RaheelFarouk/ece1895-DesignProject3/Datasheets and Reference Docs/Arduino Ethernet Shield v2.0/Images/Screenshot 2022-10-31 183120.png

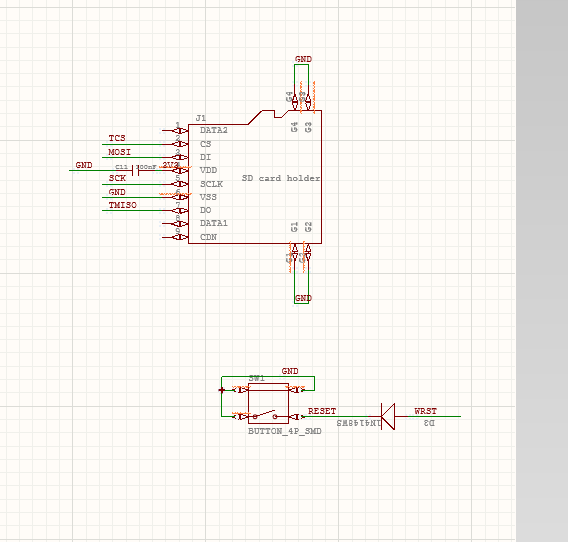
Datasheets and Reference Docs/Arduino Ethernet Shield v2.0/Images/Screenshot 2022-10-31 183120.png
