RaheelFarouk/ece1895-DesignProject3/Media/PXL_20221130_163156786.MP.jpg

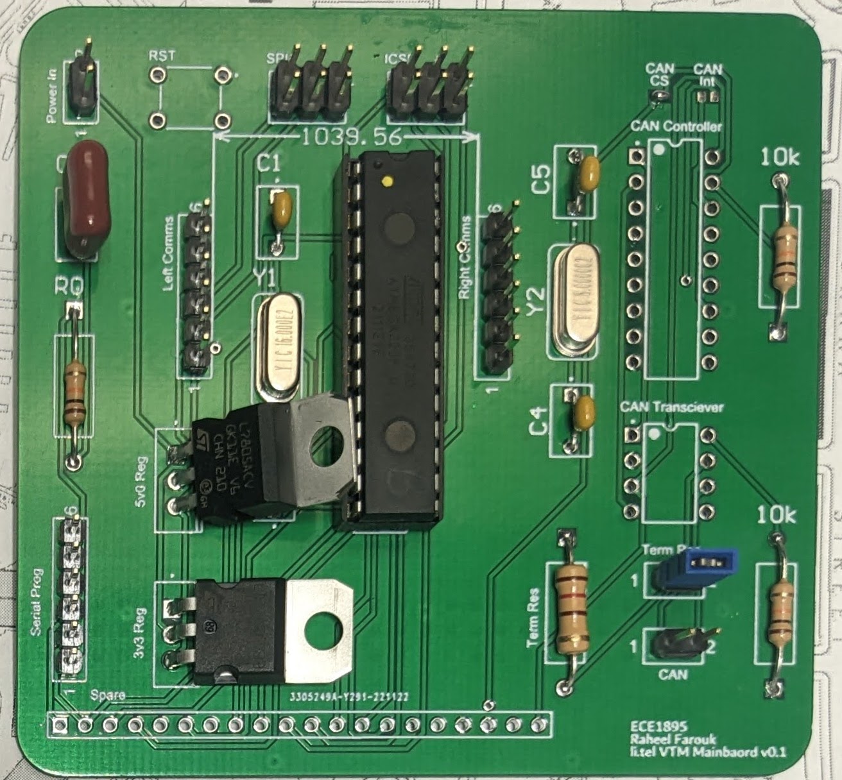
Media/PXL_20221130_163156786.MP.jpg
