RaheelFarouk/ece1895-DesignProject3/Media/PXL_20221209_193834264.jpg

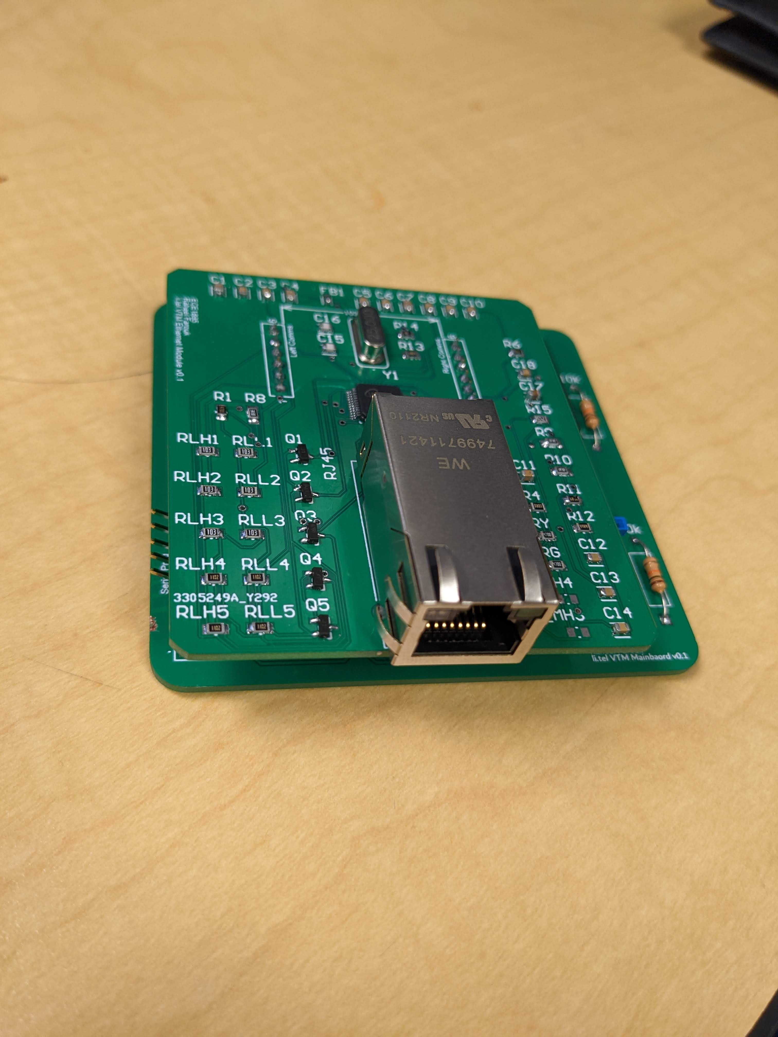
Media/PXL_20221209_193834264.jpg
