RaheelFarouk/ece1895-DesignProject3/Media/PXL_20221214_212605422.jpg

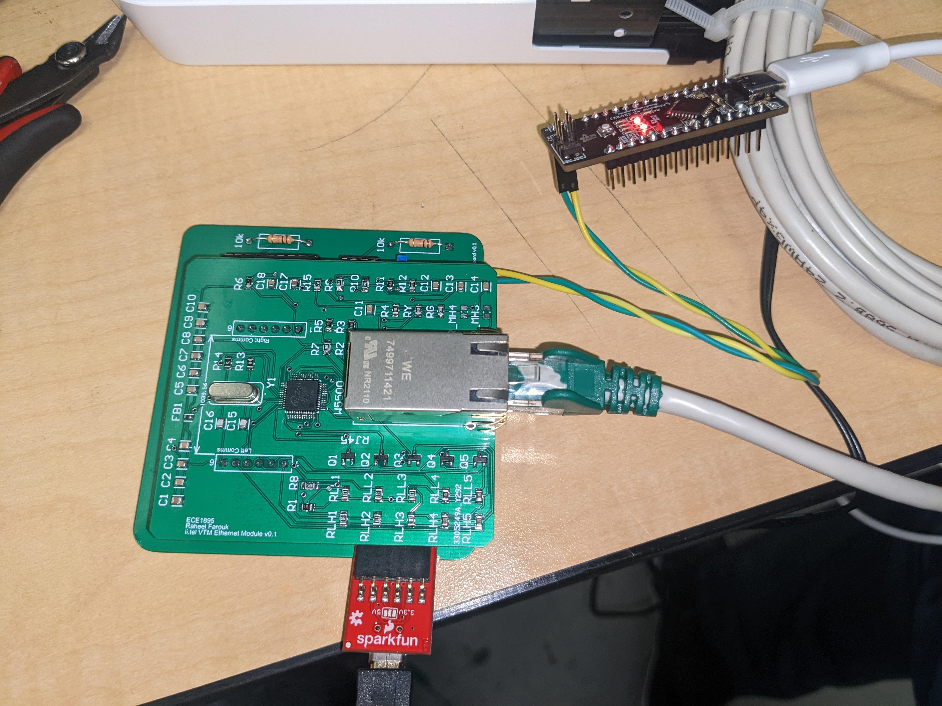
Media/PXL_20221214_212605422.jpg
