RaheelFarouk/ece1895-DesignProject3/Media/PXL_20221214_212624482.jpg

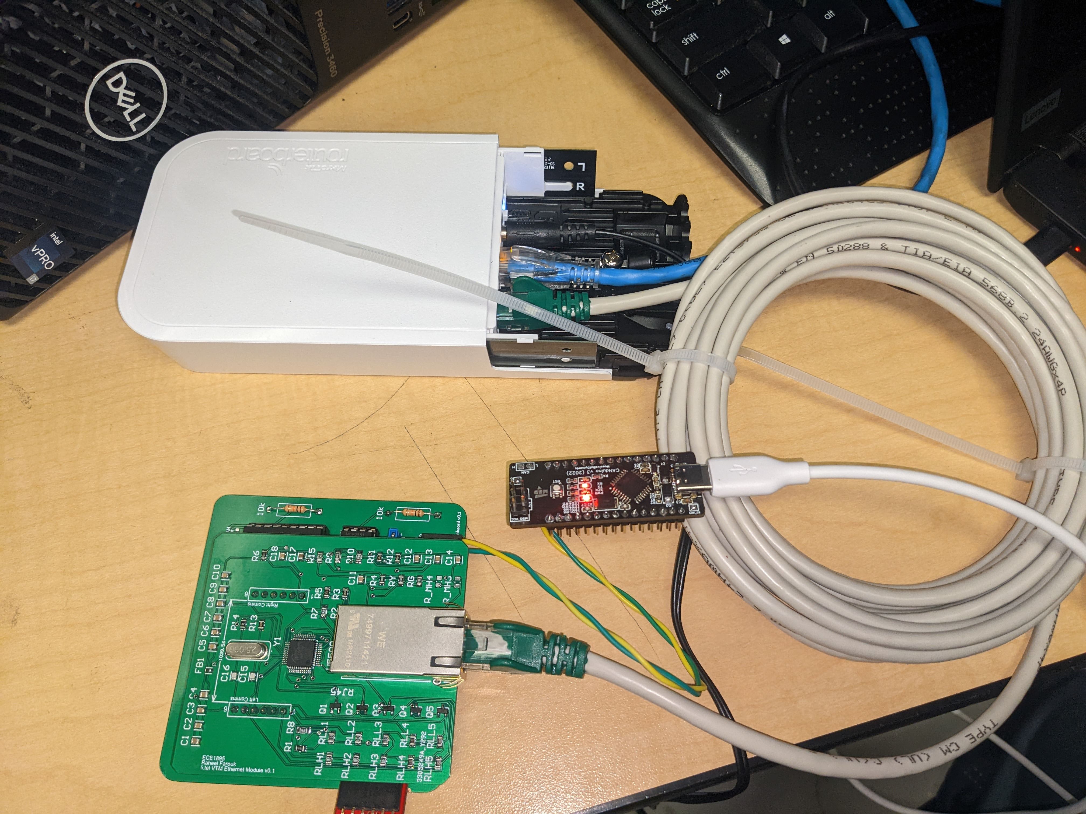
Media/PXL_20221214_212624482.jpg
