RaheelFarouk/ece1895-DesignProject3/Media/PXL_20221215_162347587.jpg

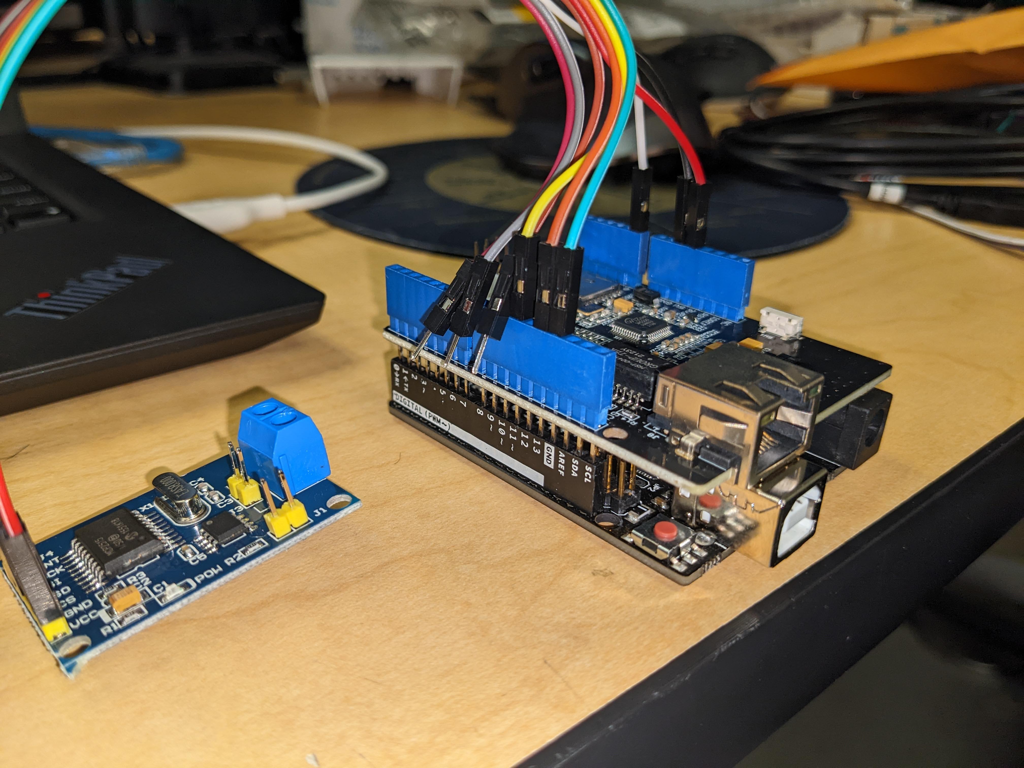
Media/PXL_20221215_162347587.jpg
