RaheelFarouk/ece1895-DesignProject3/Media/PXL_20221215_172858494.jpg

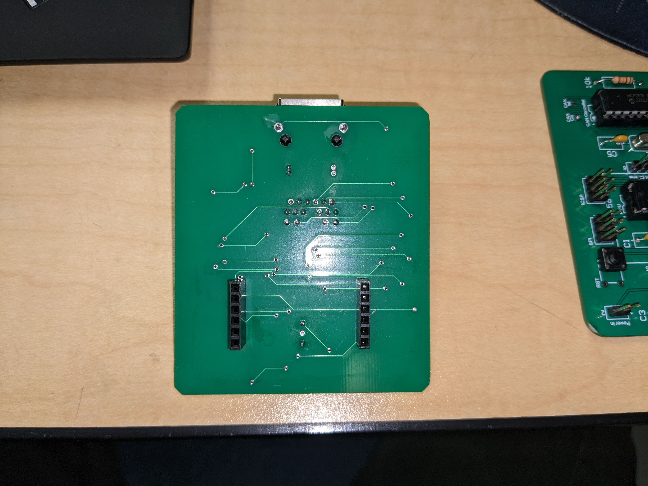
Media/PXL_20221215_172858494.jpg
