RaheelFarouk/ece1895-DesignProject3/Media/PXL_20221215_172949321.jpg

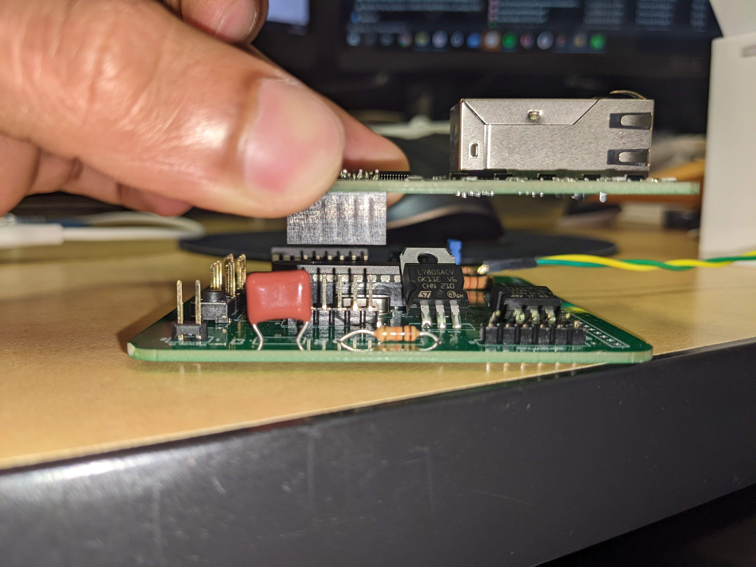
Media/PXL_20221215_172949321.jpg
