RaheelFarouk/ece1895-DesignProject3/Media/PXL_20221215_173002751.jpg

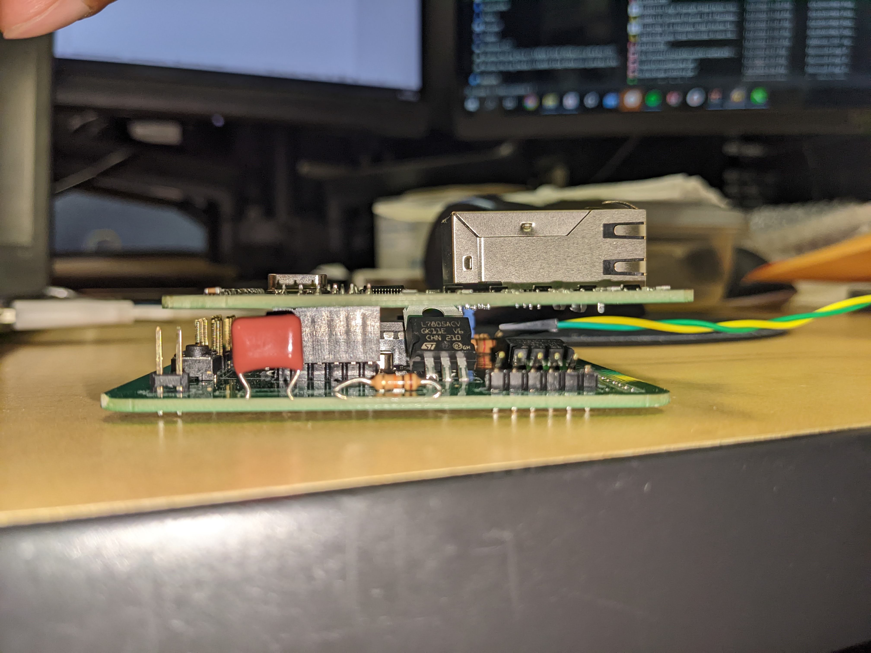
Media/PXL_20221215_173002751.jpg
