RaheelFarouk/ece1895-DesignProject3/Media/ReadmeImages/image007.png

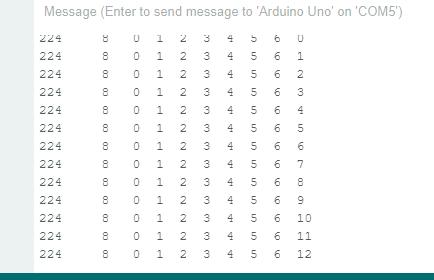
Media/ReadmeImages/image007.png
