RaheelFarouk/ece1895-DesignProject3/Media/ReadmeImages/image011.png

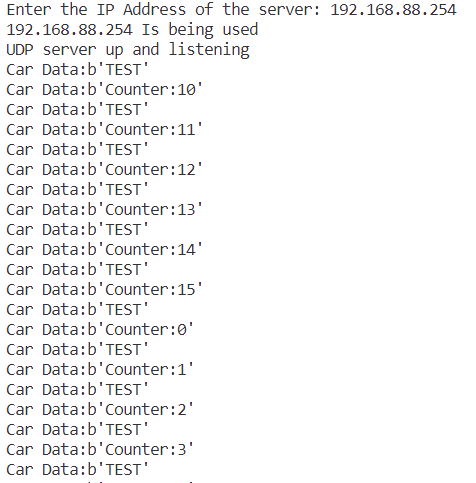
Media/ReadmeImages/image011.png
