RaheelFarouk/ece1895-DesignProject3/Media/ReadmeImages/image013.png

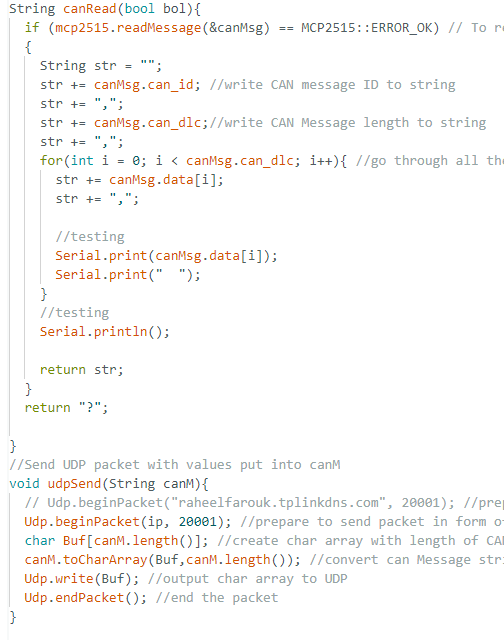
Media/ReadmeImages/image013.png
