RaheelFarouk/ece1895-DesignProject3/Media/ReadmeImages/image015.png

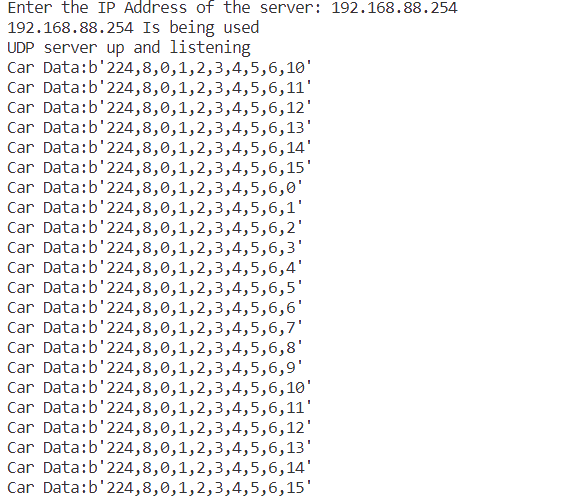
Media/ReadmeImages/image015.png
