RaheelFarouk/ece1895-DesignProject3/Media/ReadmeImages/image019.png

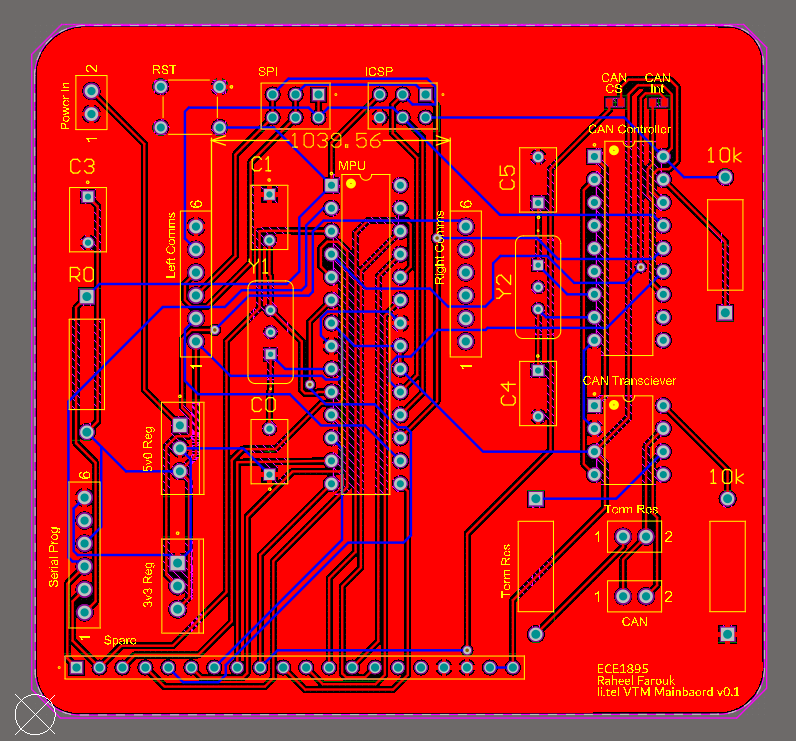
Media/ReadmeImages/image019.png
