RaheelFarouk/ece1895-DesignProject3/Media/ReadmeImages/image037.png

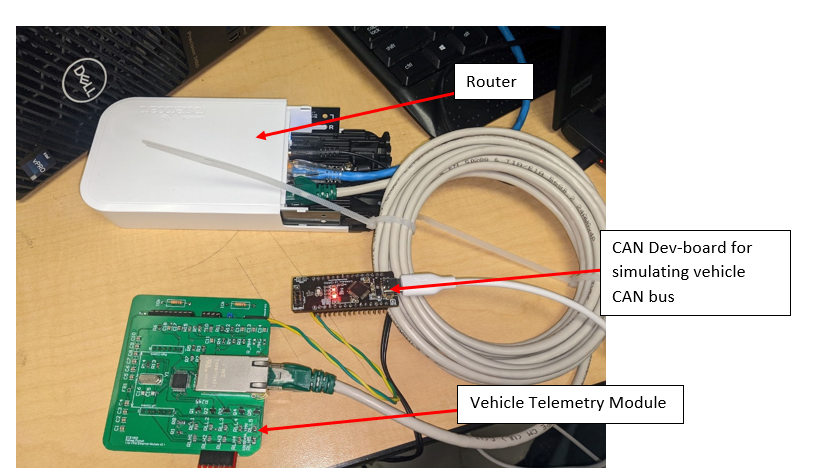
Media/ReadmeImages/image037.png
