RaheelFarouk/ece1895-DesignProject3/Media/ReadmeImages/image041.png

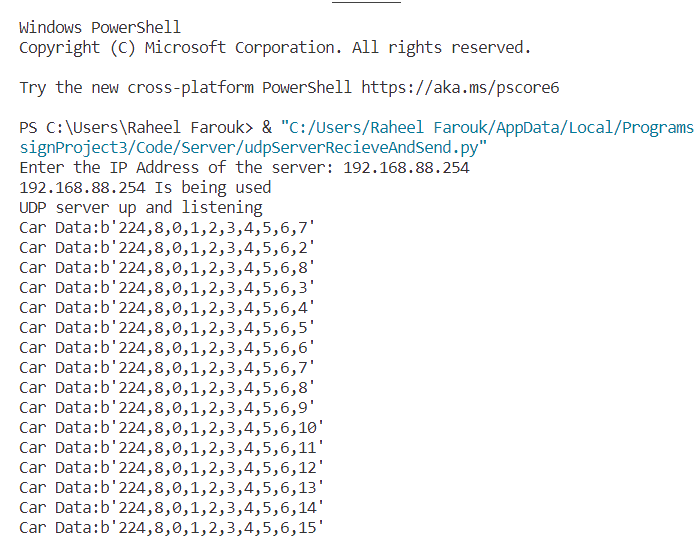
Media/ReadmeImages/image041.png
