RaheelFarouk/ece1895-DesignProject3/Media/ReadmeImages/image045.jpg

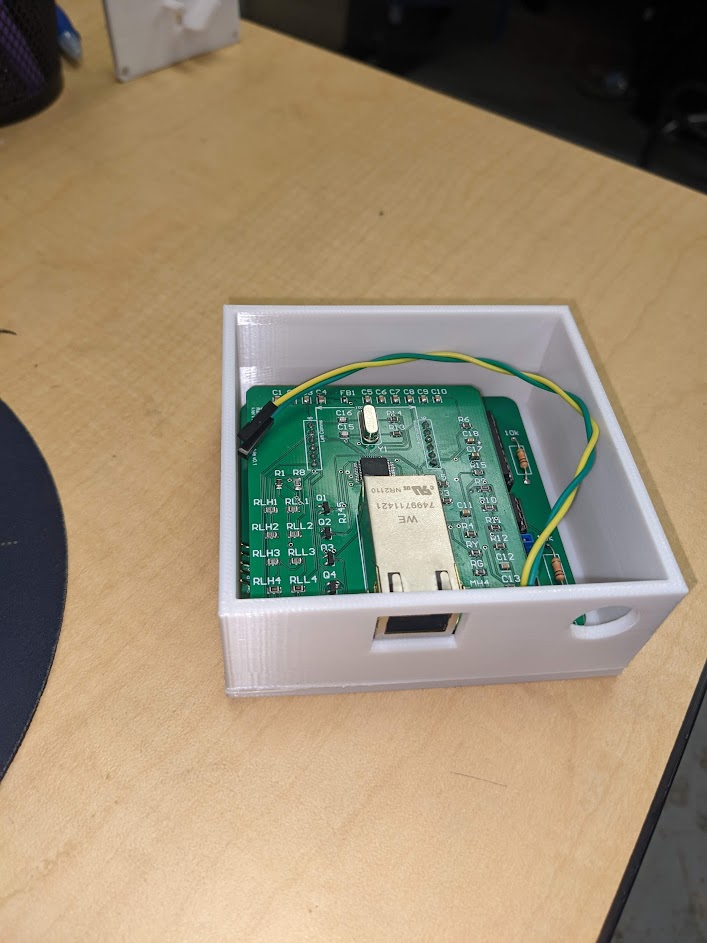
Media/ReadmeImages/image045.jpg
