RaheelFarouk/ece1895-DesignProject3/Media/ReadmeImages/image047.jpg

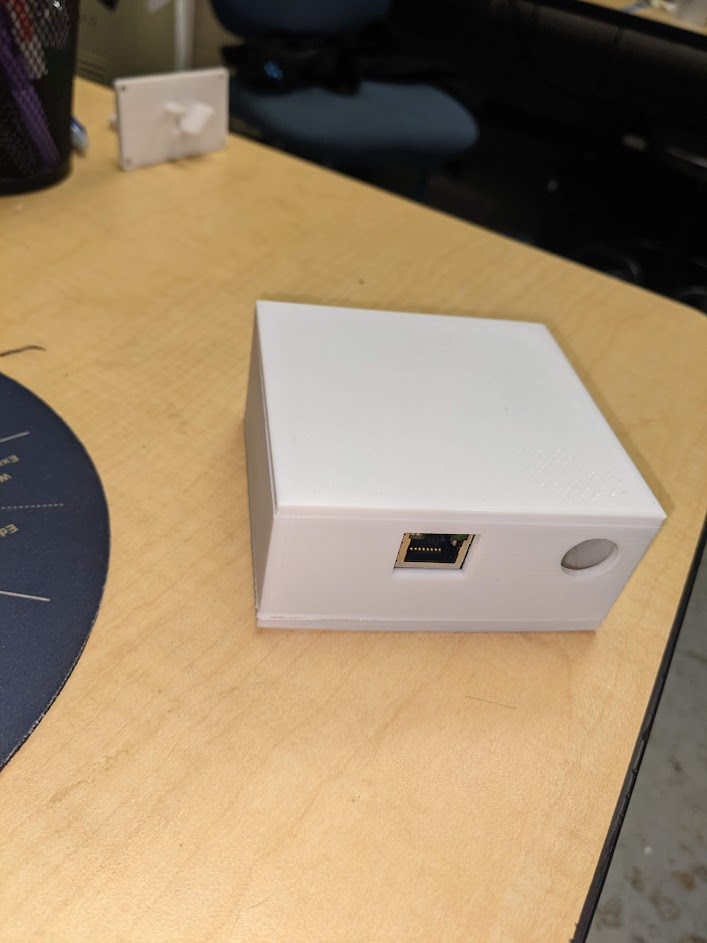
Media/ReadmeImages/image047.jpg
