RaheelFarouk/ece1895-DesignProject3/Hardware/CAD/body.SLDPRT

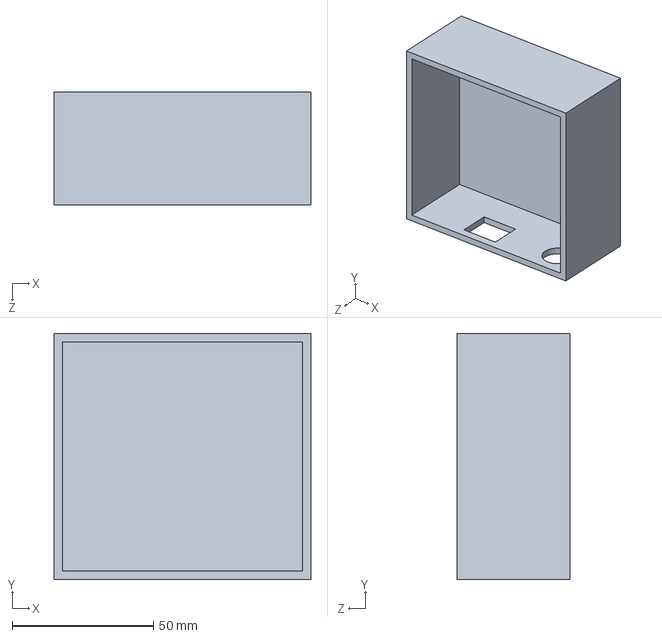
[picture p49: CAD file, 2022-12-16]
Hardware/CAD/body.SLDPRT
91.0 x 87.2 x 40.0 mm
