RaheelFarouk/ece1895-DesignProject3/Hardware/CAD/Microprocessor Module (328).step

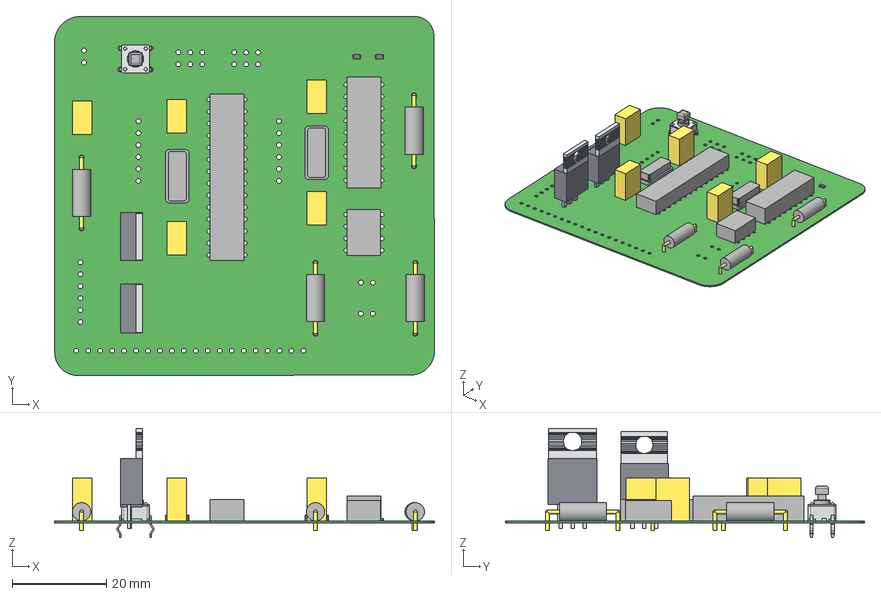
[picture p50: CAD file, 2022-12-16]
Hardware/CAD/Microprocessor Module (328).step
80.7 x 76.2 x 23.2 mm
Extruded x 94
TL1105BODY
1105-COVER-PLATE
TL1105-3301ACTUATOR SP & JA 2_8
TL1105CONTACTDOME
Mid_Body x 2
Mark x 2
