RaheelFarouk/ece1895-DesignProject3/Hardware/CAD/VTM Ethernet Module.step

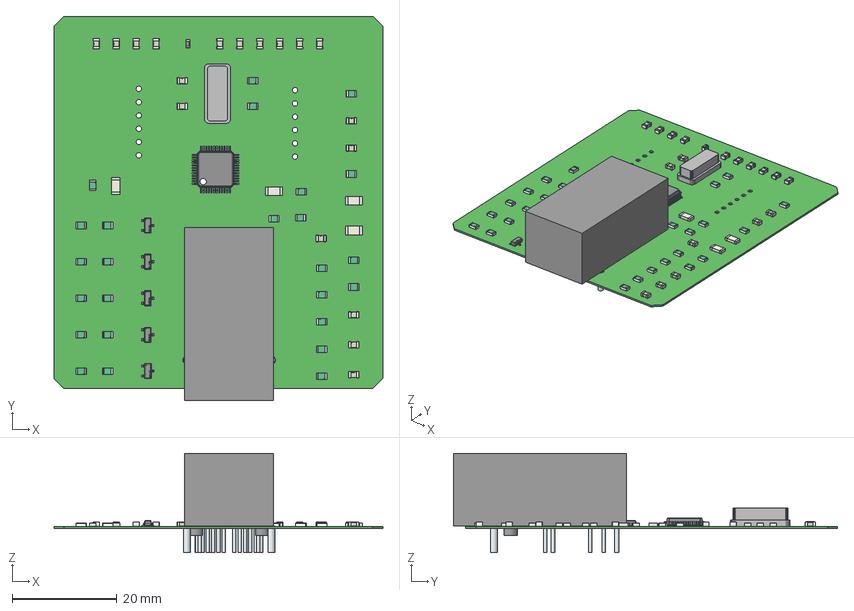
[picture p51: CAD file, 2022-12-16]
Hardware/CAD/VTM Ethernet Module.step
62.9 x 73.4 x 19.0 mm
Extruded x 14
TE connectivity Logo 1 (2) x 25
Lugs
Leads
ON Semi Logo - withoutPN x 5
ON Semi Logo - withoutPN - Copy x 5
side x 2
Murata
Cap_KEMET_C0805C472J3HAC_eec x 54
