RaheelFarouk/ece1895-DesignProject3/Hardware/CAD/lid.SLDPRT

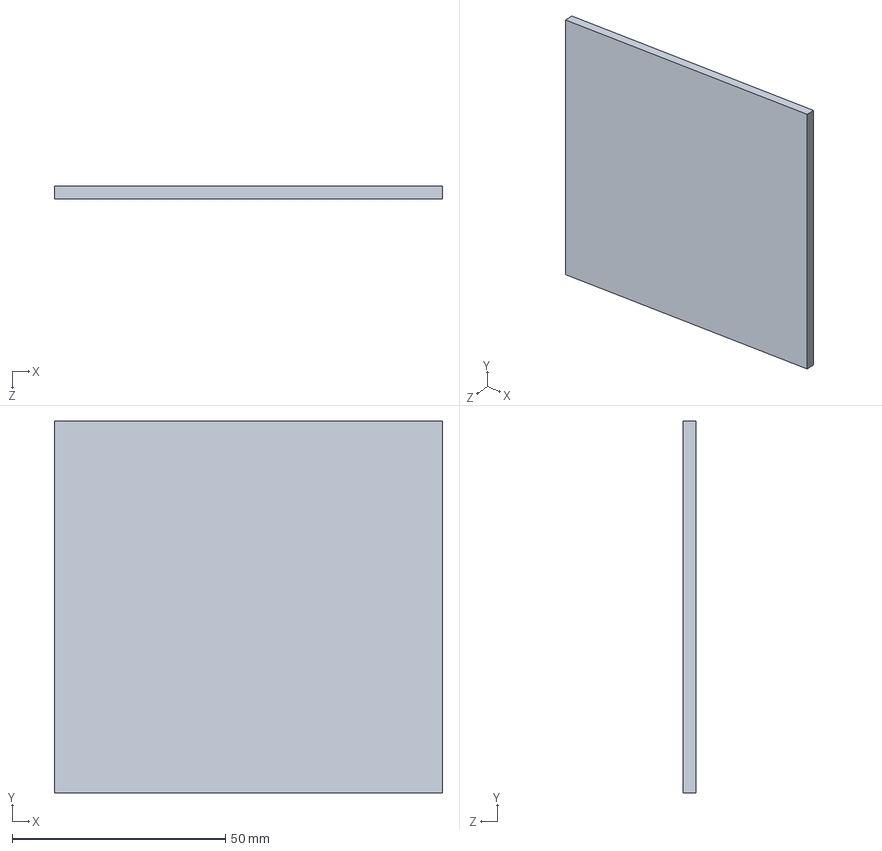
[picture p52: CAD file, 2022-12-16]
Hardware/CAD/lid.SLDPRT
91.0 x 87.2 x 3.00 mm
